langchr86/homesensor/hardware/case_outdoor/images/Entwurf-1.1d.png

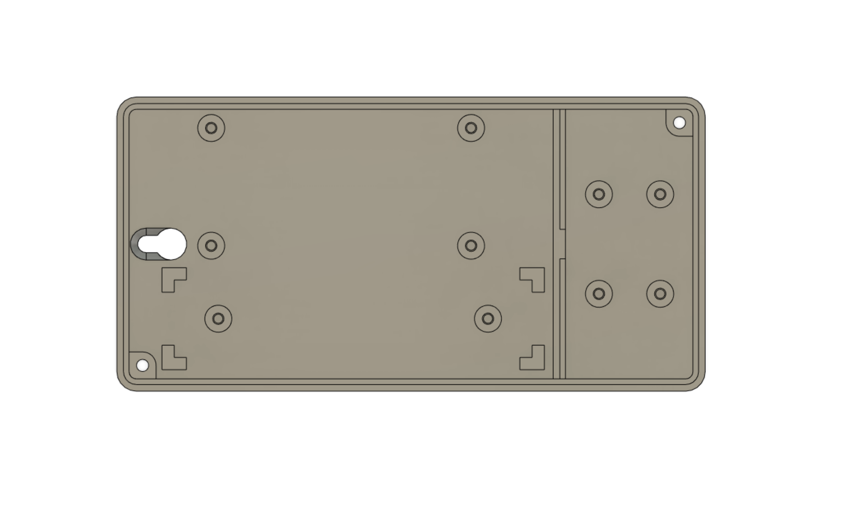
hardware/case_outdoor/images/Entwurf-1.1d.png
