langchr86/homesensor/hardware/case_outdoor/images/Microcontroller.png

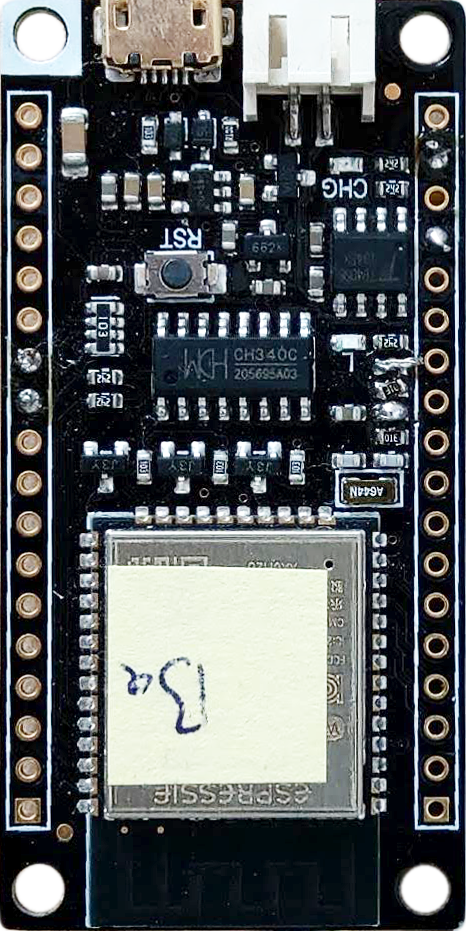
hardware/case_outdoor/images/Microcontroller.png
