langchr86/homesensor/software/src/infrastructure/device_factory.cpp

#include "infrastructure/device_factory.h"

#include "sensors/scd30.h"
#include "sensors/shtc3.h"

DeviceFactory::DeviceFactory(const std::chrono::seconds &readout_interval, const std::chrono::seconds &expire_timeout)
    : logger_("DeviceFactory"), readout_interval_(readout_interval), expire_timeout_(expire_timeout)
{
}

std::shared_ptr<SensorInterface> DeviceFactory::CreateDevice(const DeviceConfig &config, ADC *adc, TwoWire *wire, Connection *connection, Power *power)
{
    connection->SetOwnStaticIp(config.ip_address);

    std::shared_ptr<SensorInterface> sensor;
    switch (config.type)
    {
    case DeviceType::kShtc3:
        sensor = std::make_shared<Shtc3>(adc, wire, connection, power, config.name.c_str(), config.unique_id.c_str(), expire_timeout_);
        break;
    case DeviceType::kScd30:
        sensor = std::make_shared<Scd30>(adc, wire, connection, power, config.name.c_str(), config.unique_id.c_str(), expire_timeout_);
        break;
    }

    return sensor;
}
